Ragh7av/Macropad/IMAGES/Screenshot 2026-06-19 180728.png

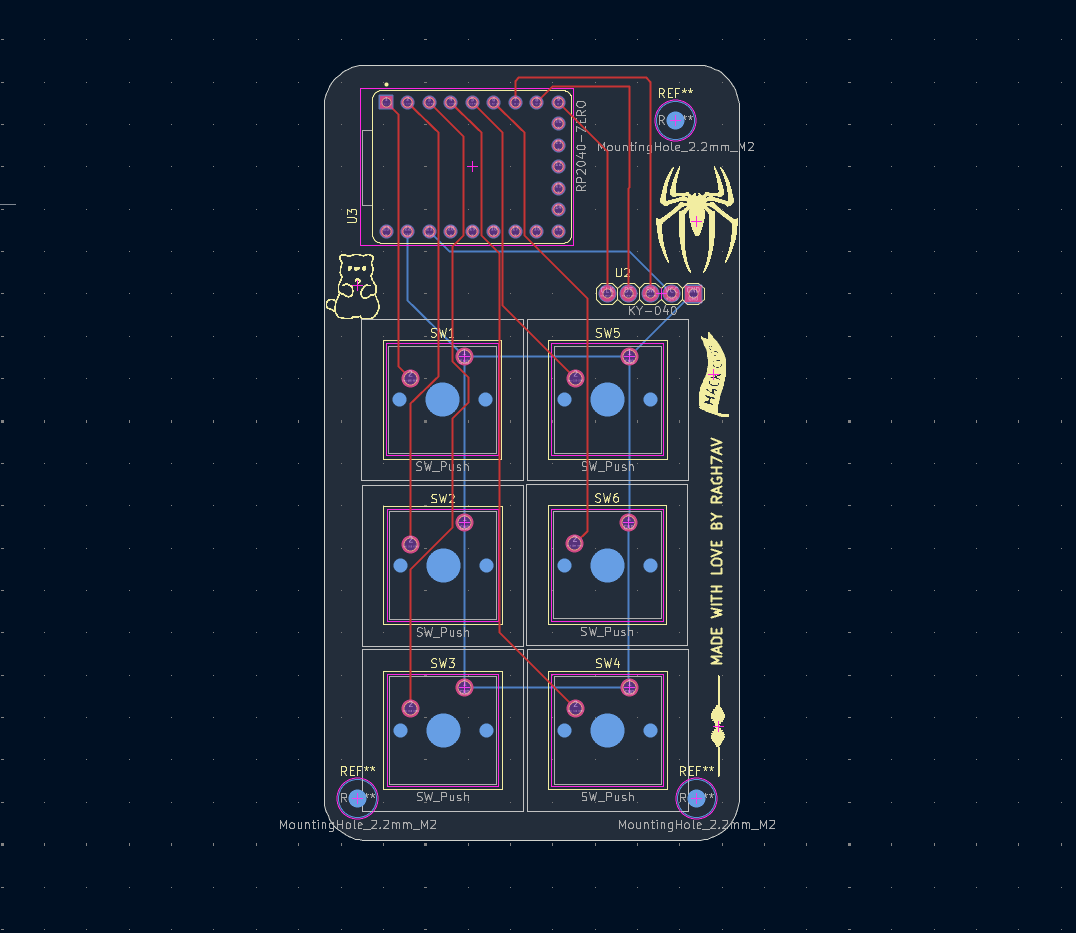
IMAGES/Screenshot 2026-06-19 180728.png
