Ragh7av/Macropad/IMAGES/Screenshot 2026-06-19 184425.png

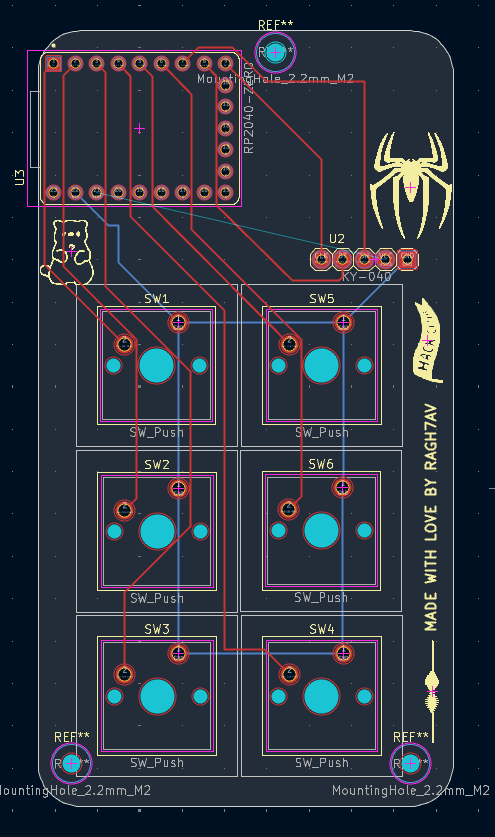
IMAGES/Screenshot 2026-06-19 184425.png
