Ragh7av/Macropad/IMAGES/Screenshot 2026-06-20 013915.png

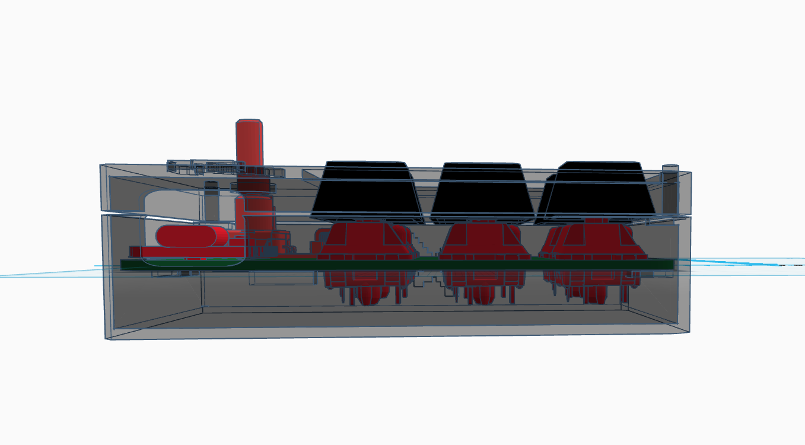
IMAGES/Screenshot 2026-06-20 013915.png
