Ragh7av/Macropad/IMAGES/Screenshot 2026-06-20 013951.png

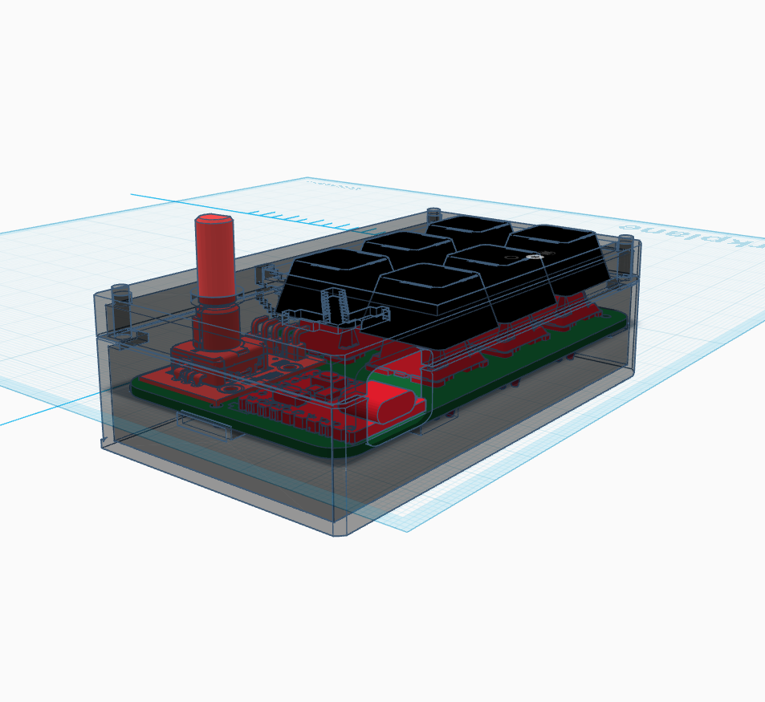
IMAGES/Screenshot 2026-06-20 013951.png
