Ragh7av/Macropad/IMAGES/Screenshot 2026-06-20 014122.png

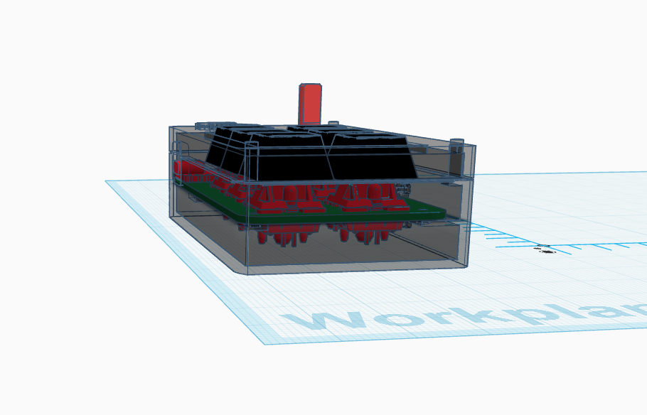
IMAGES/Screenshot 2026-06-20 014122.png
