Ragh7av/Macropad/IMAGES/Screenshot 2026-06-20 021821.png

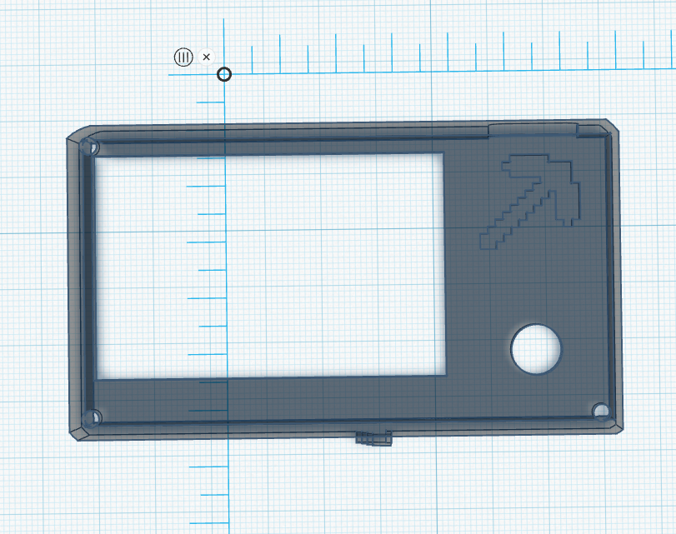
IMAGES/Screenshot 2026-06-20 021821.png
