Ragh7av/Macropad/IMAGES/Screenshot 2026-06-20 021831.png

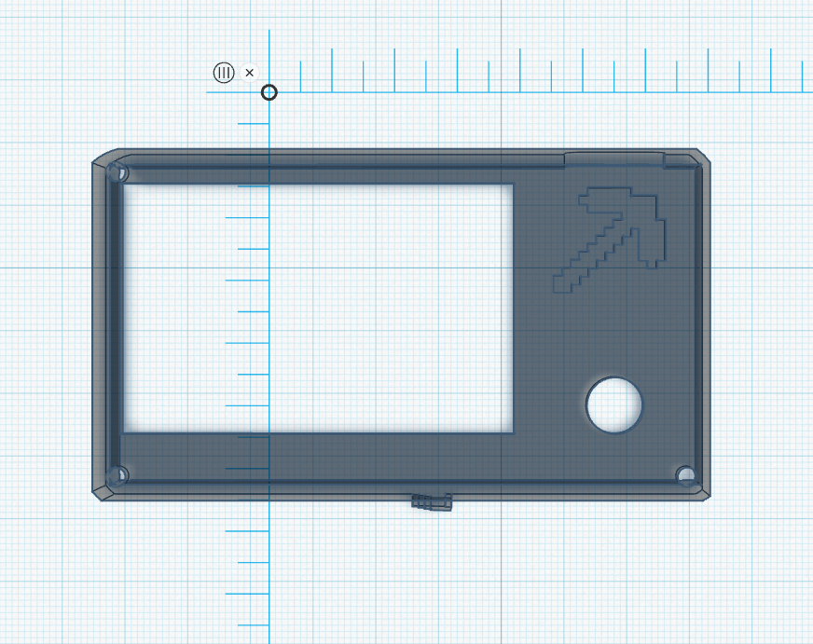
IMAGES/Screenshot 2026-06-20 021831.png
