Ragh7av/Macropad/IMAGES/Screenshot 2026-06-20 021850.png

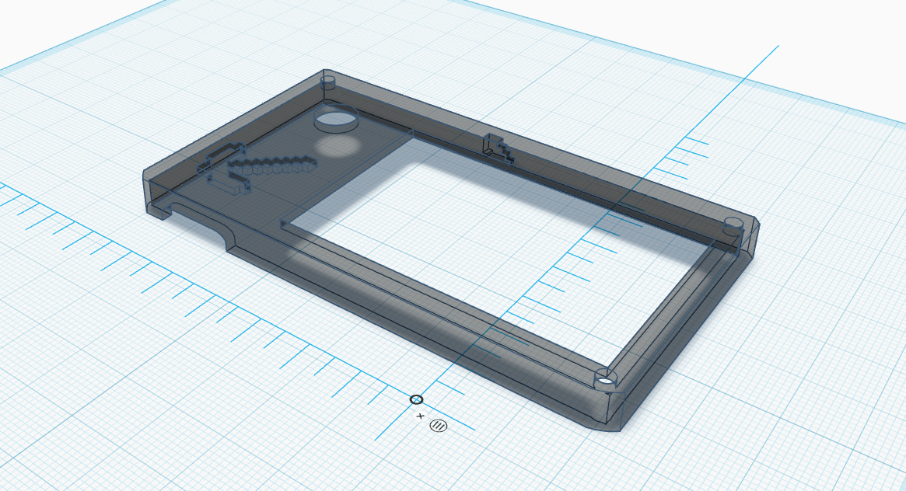
IMAGES/Screenshot 2026-06-20 021850.png
