Ragh7av/Macropad/IMAGES/Screenshot 2026-06-20 021950.png

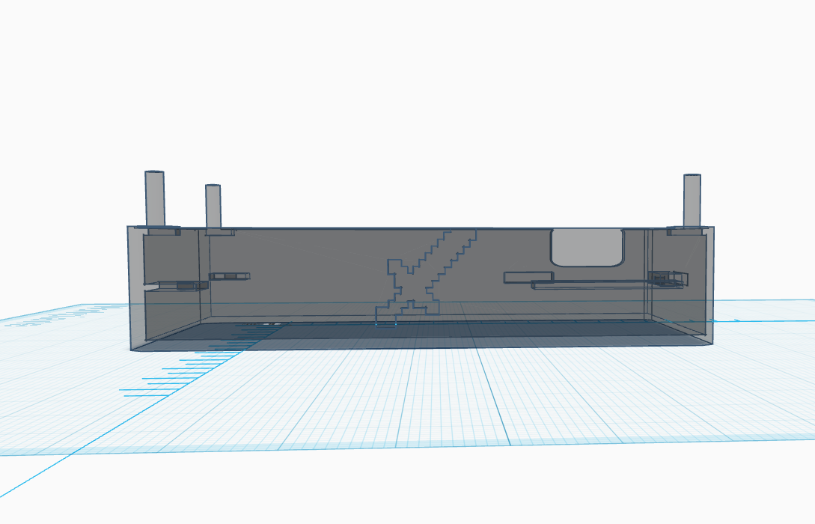
IMAGES/Screenshot 2026-06-20 021950.png
