Ragh7av/Macropad/IMAGES/Screenshot 2026-06-20 021958.png

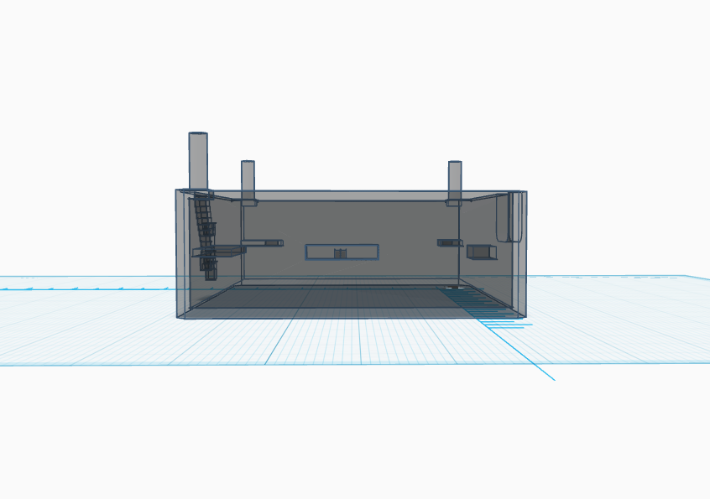
IMAGES/Screenshot 2026-06-20 021958.png
