Ragh7av/Macropad/IMAGES/Screenshot 2026-06-20 022014.png

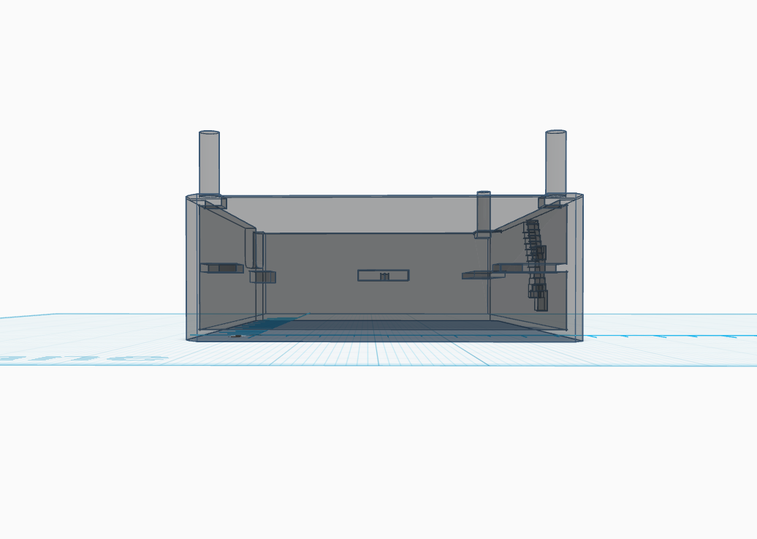
IMAGES/Screenshot 2026-06-20 022014.png
