Ragh7av/Macropad/PCB/Macropad.png

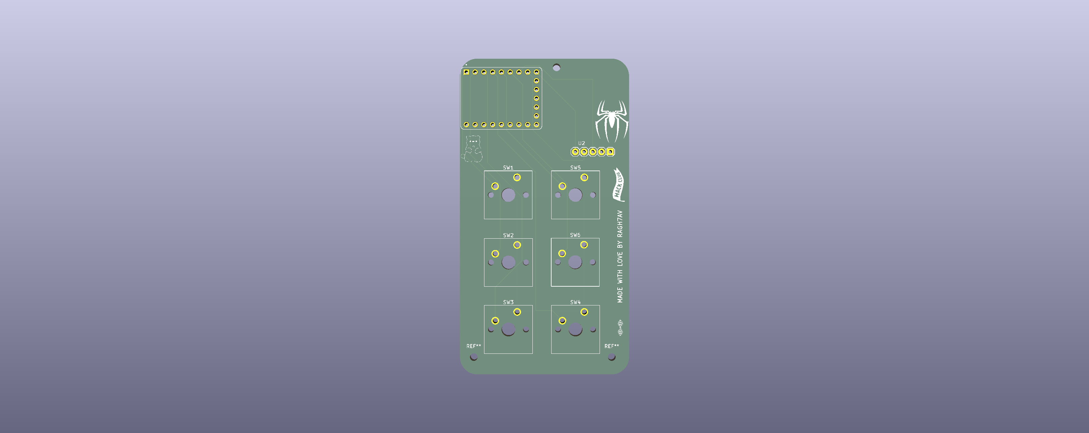
PCB/Macropad.png
