Ragh7av/Macropad/ZINE/Zine.png

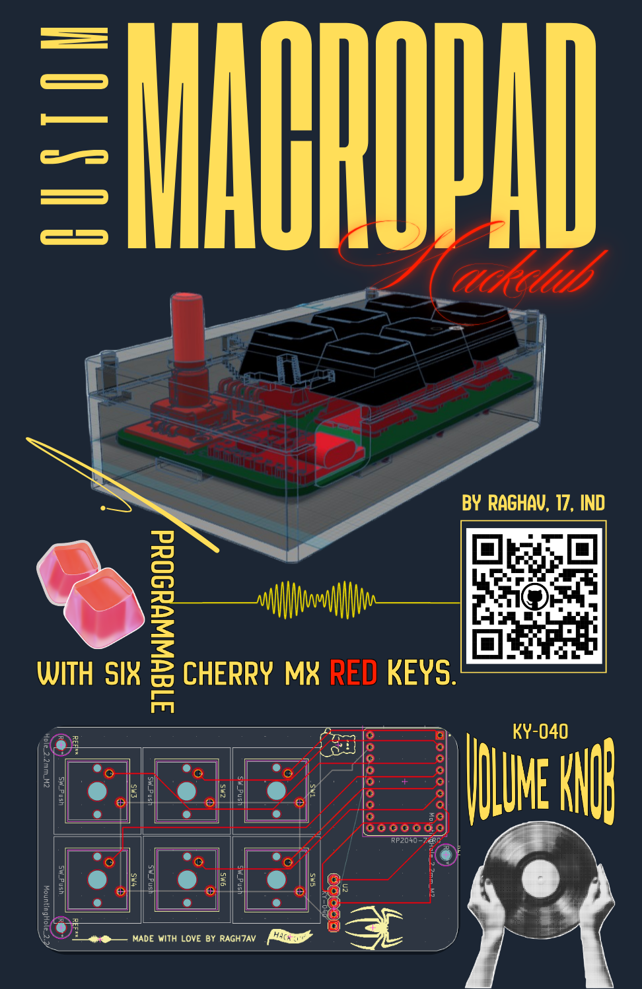
ZINE/Zine.png
