Ragh7av/Macropad/ASSEMBLY/Screenshot 2026-06-27 155041.png

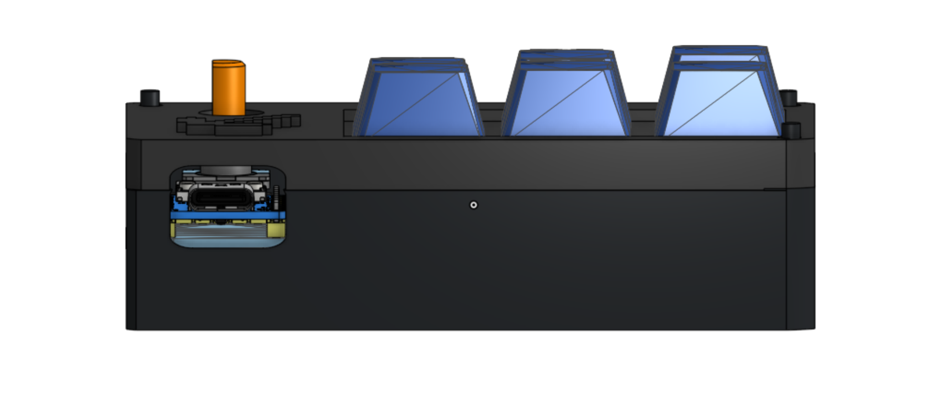
ASSEMBLY/Screenshot 2026-06-27 155041.png
