Ragh7av/Macropad/ASSEMBLY/Screenshot 2026-06-27 155052.png

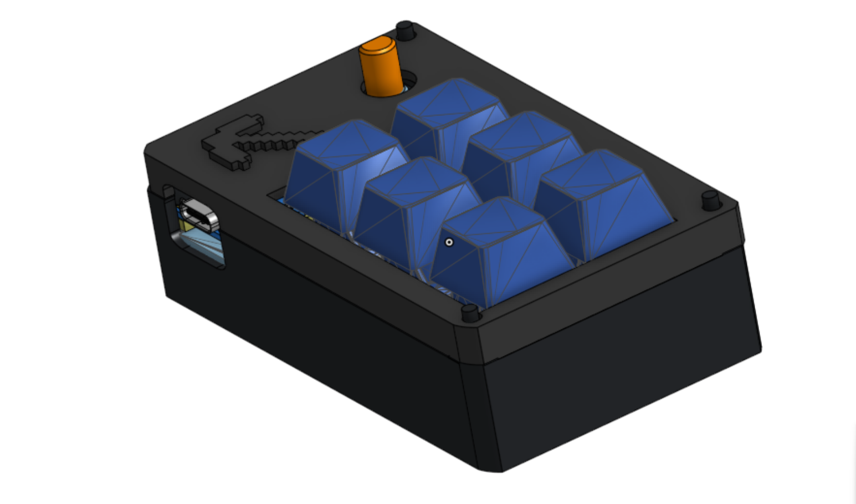
ASSEMBLY/Screenshot 2026-06-27 155052.png
