Ragh7av/Macropad/ASSEMBLY/Screenshot 2026-06-27 155108.png

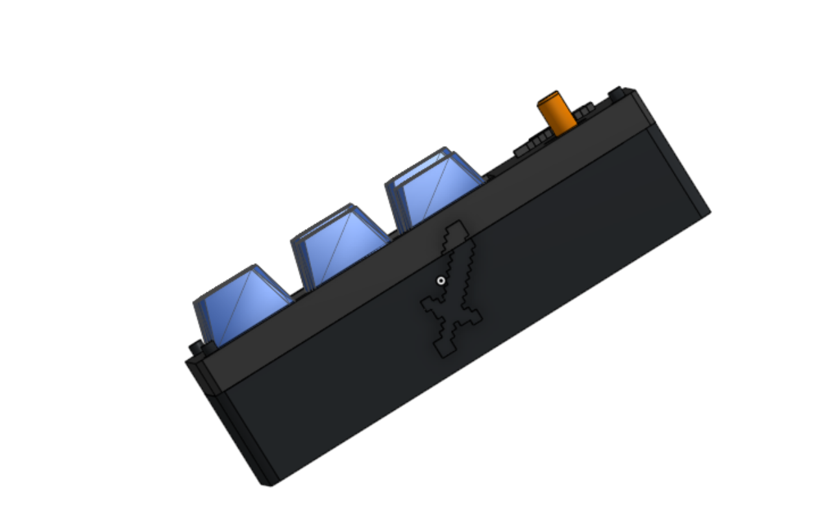
ASSEMBLY/Screenshot 2026-06-27 155108.png
